Heimdallr-Systems/Circuit-Board/Simulations/LTspice/Motor Current Spike.asc

S1: sw; MYSW
V1: voltage; 7
V2: voltage; PULSE(0 1 1 1f 1f 200 200 1)
V3: voltage; 0; Rser=0
X1: Servo
Named nets: 0
.tran 0 5
.model MYSW SW(Ron=1 Roff=1Meg Vt=.5 Vh=-.4)
