Heimdallr-Systems/Circuit-Board/Simulations/LTspice/Reverse Voltage Protection.asc

D1: schottky; D1n4004rl
R1: res; 10k
R2: res; R=abs(V(vcc)/{I})+1m
U4: SQP50P03-07
V1: voltage; 0
Named nets: 0, LOAD, VCC
.step param I 1 13 1 ; Step through possible currents
Percent Diff Equation
(abs(V(spqload)/V(vcc))-abs(V(IRFLOAD)/V(vcc)))/(0.5*(abs(V(spqload)/V(vcc))+abs(V(IRFLOAD)/V(vcc))))*100
Resistor varies with voltage
to keep current constant. 
adding 1 miliohm means that
there is never a resistance of 0. 
Without it, at 0V, we have 0 ohm
and the current plots have a big spike
.lib SQP50P03-07_PS_Rev_A.LIB
.inc 1n4004rl.lib ; Include specific Diode. Obtained from ON Semiconductor Site
.dc V1 -10 10 0.01 ; DC Sweep from -10V to -1V, 0.5V increment
