Heimdallr-Systems/Circuit-Board/Simulations/LTspice/Servo.asc

B1: bi; I=I(V_SENSE_2)
Back_EMF: bv; V=I(V_SENSE_2)*K_emf
C1: cap; 1
L_inertia: ind; {L_inertia}; Rser=0 Rpar=0
L_motor: ind; {L_Motor}
R3: res; 1
R_loss: res; {R_loss}
R_motor: res; {R_Motor}
V_SENSE_1: voltage; 0; Rser=0
V_SENSE_2: voltage; 0; Rser=0
V_torque: bv; V=I(V_SENSE_1)
Named nets: 0, +, Angle, -
Design from
https://www.precisionmicrodrives.com/content/ab-025-using-spice-to-model-dc-motors/
.PARAM K_t = 900u K_EMF = 900u L_Motor = 50u R_motor = 5.5  R_loss = 300n L_inertia = 15n
Motor
Mechanical Model
Angle Sensor
